skyylarkk/projet3A/Modele_Solidworks/Pince/Pièce1.SLDPRT

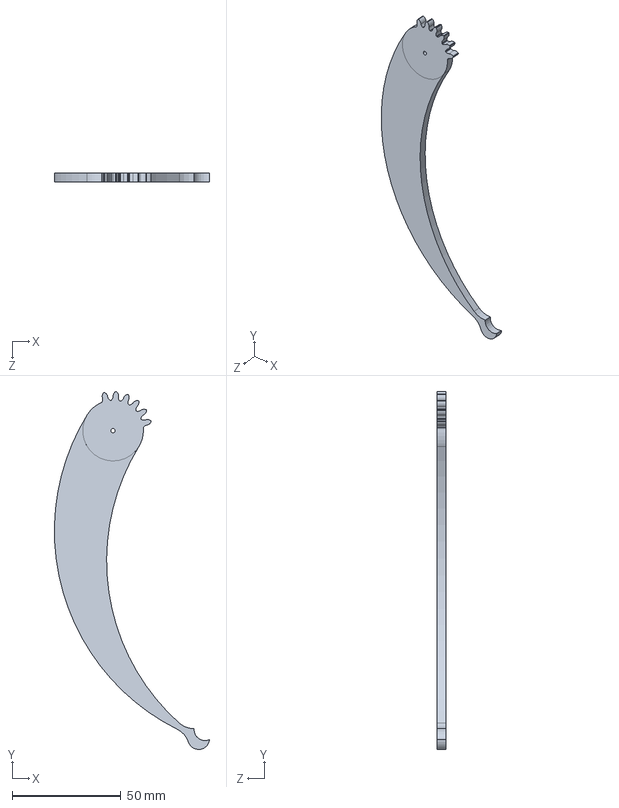
[picture p39: CAD file, 2022-12-07]
Modele_Solidworks/Pince/Pièce1.SLDPRT
71.2 x 164.3 x 4.00 mm
