skyylarkk/projet3A/Modele_Solidworks/Avant-bras/Support_axe_2.SLDPRT

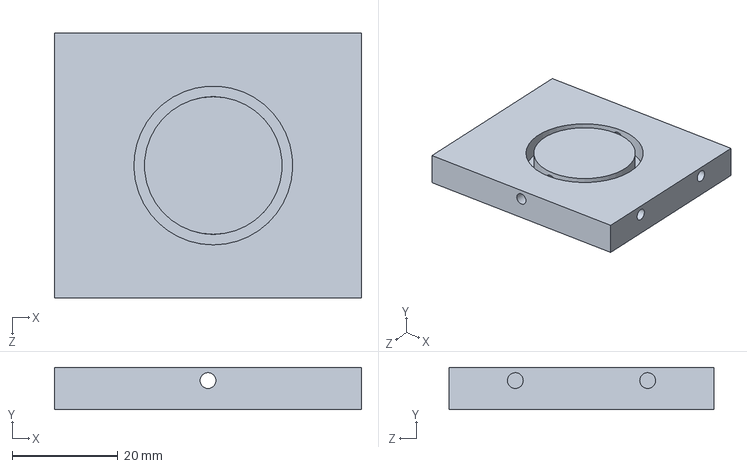
[picture p40: CAD file, 2022-12-26]
Modele_Solidworks/Avant-bras/Support_axe_2.SLDPRT
58.0 x 8.00 x 50.0 mm
