skyylarkk/projet3A/Modele_Solidworks/Base/roue sur pignon moteur.SLDPRT

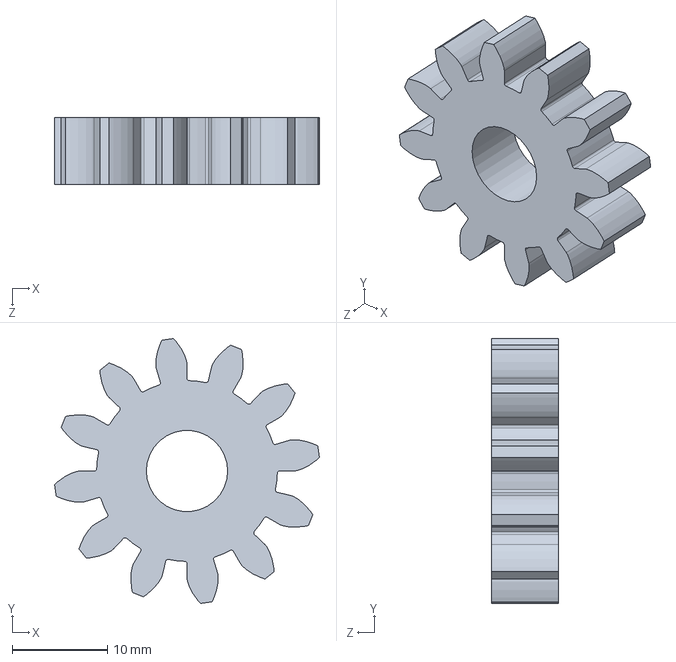
[picture p41: CAD file, 2023-01-16]
Modele_Solidworks/Base/roue sur pignon moteur.SLDPRT
27.9 x 27.9 x 7.00 mm
