skyylarkk/projet3A/Modele_Solidworks/Epaule/roue satellite.SLDPRT

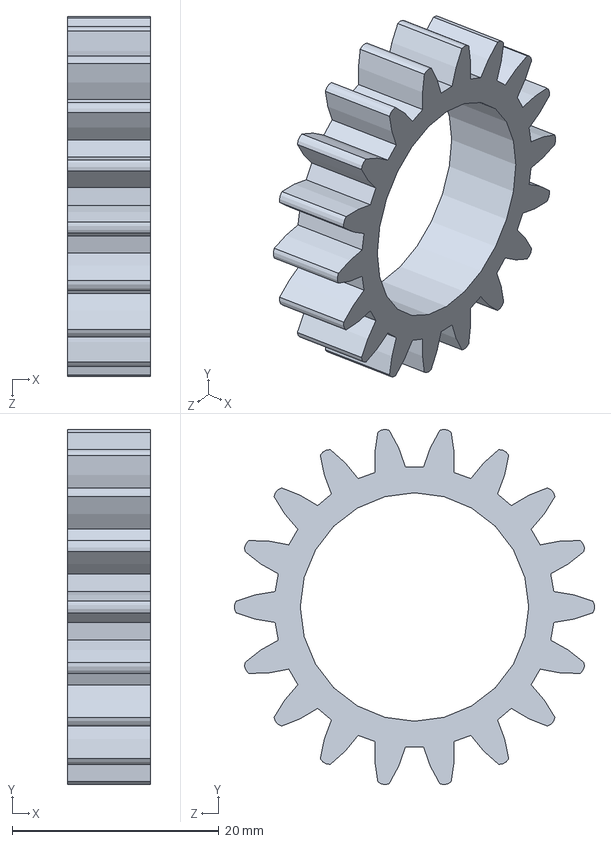
[picture p42: CAD file, 2023-01-16]
Modele_Solidworks/Epaule/roue satellite.SLDPRT
8.00 x 34.4 x 34.8 mm
