skyylarkk/projet3A/Modele_Solidworks/Pince/Bloqueur.SLDPRT

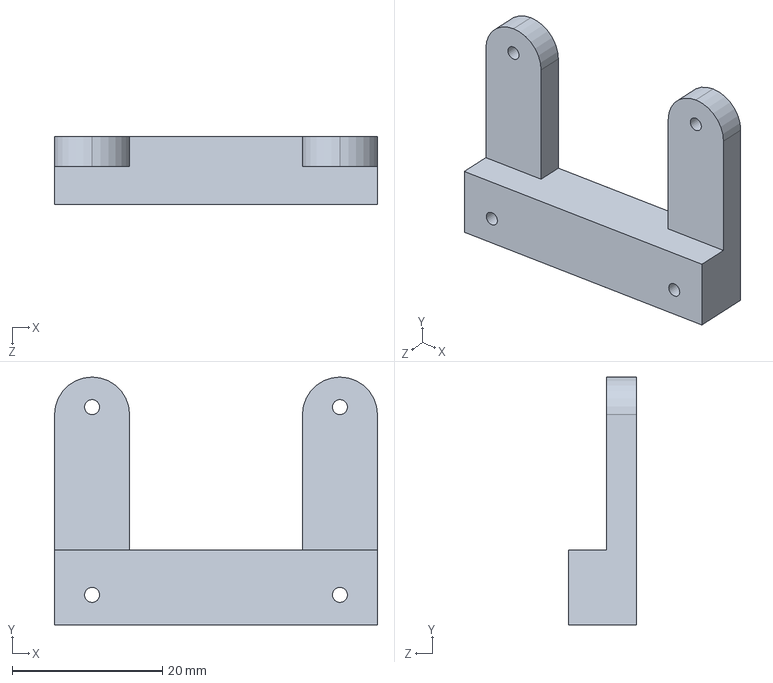
[picture p43: CAD file, 2022-12-07]
Modele_Solidworks/Pince/Bloqueur.SLDPRT
43.0 x 33.0 x 9.00 mm
