skyylarkk/projet3A/Modele_Solidworks/Poignet/Côté_2_ext - Copie.SLDPRT

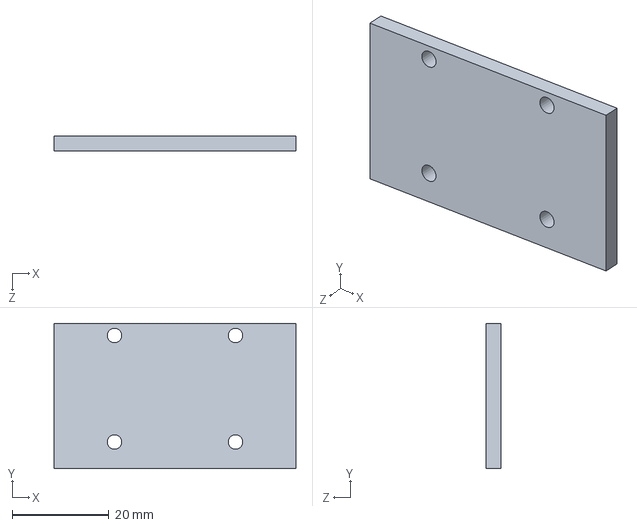
[picture p44: CAD file, 2022-12-11]
Modele_Solidworks/Poignet/Côté_2_ext - Copie.SLDPRT
50.0 x 30.0 x 3.00 mm
