skyylarkk/projet3A/Modele_Solidworks/Bras/Support_axe.SLDPRT

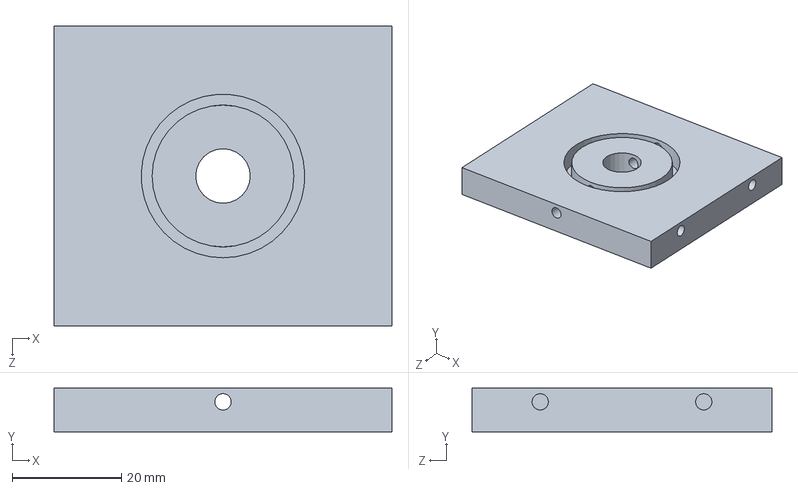
[picture p45: CAD file, 2023-01-06]
Modele_Solidworks/Bras/Support_axe.SLDPRT
62.0 x 8.00 x 55.0 mm
