skyylarkk/projet3A/Modele_Solidworks/Epaule/Couronne train epi.SLDPRT

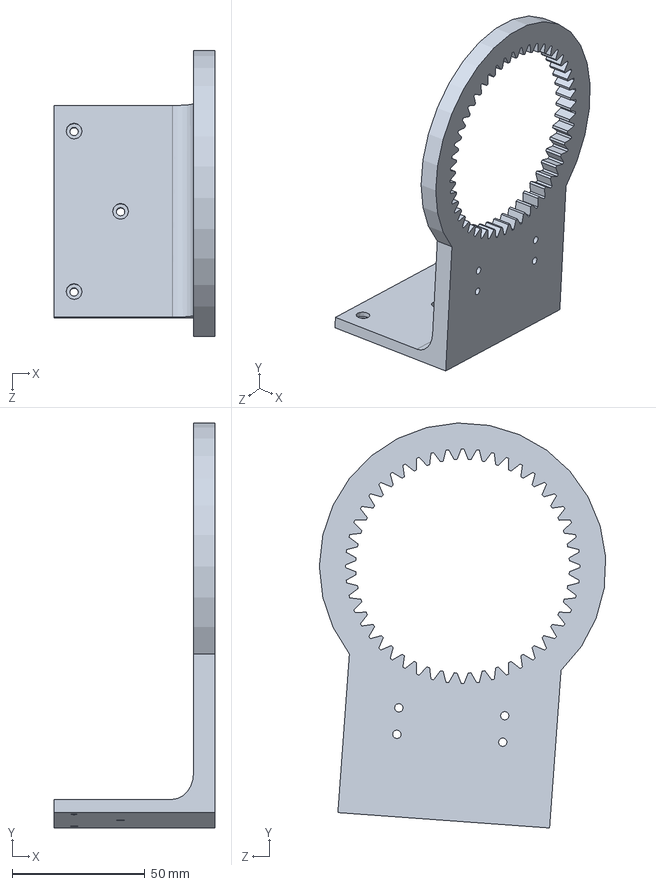
[picture p46: CAD file, 2023-01-16]
Modele_Solidworks/Epaule/Couronne train epi.SLDPRT
60.5 x 152.6 x 107.9 mm
