skyylarkk/projet3A/Modele_Solidworks/Poignet/Support_axe_2.SLDPRT

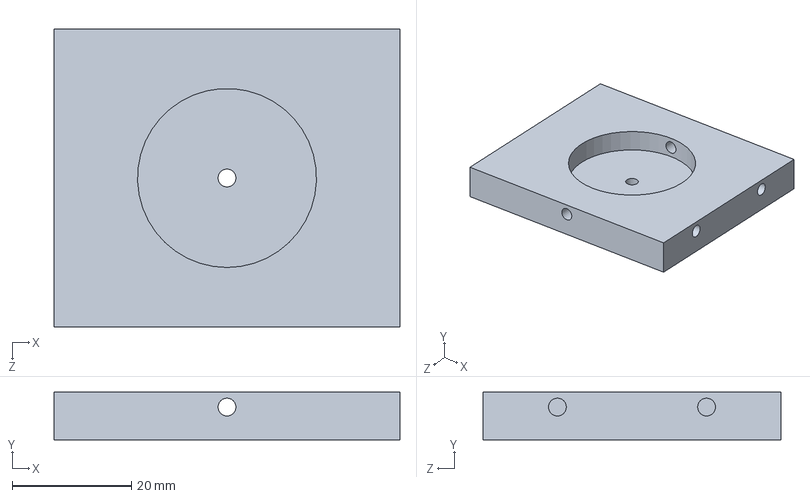
[picture p47: CAD file, 2022-12-11]
Modele_Solidworks/Poignet/Support_axe_2.SLDPRT
58.0 x 8.00 x 50.0 mm
