skyylarkk/projet3A/Modele_Solidworks/Base/bearing_61804_2_02.SLDPRT

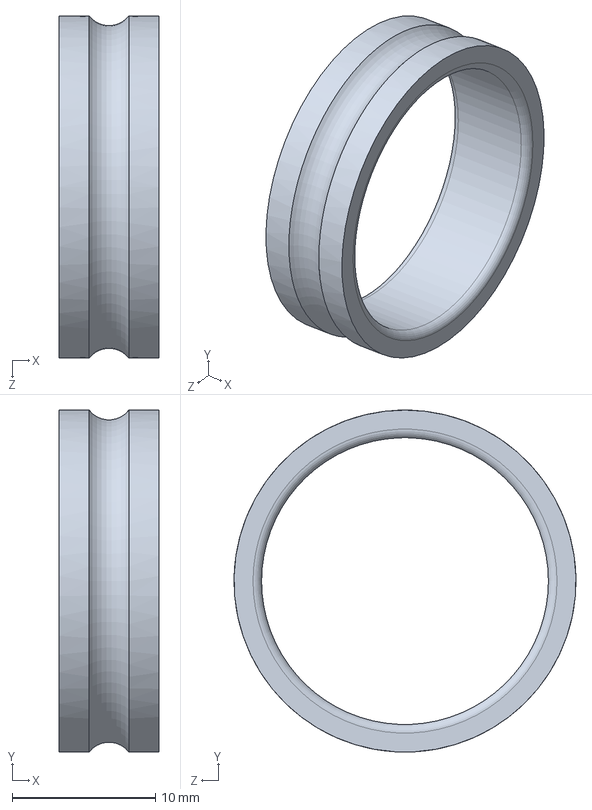
[picture p48: CAD file, 2023-01-10]
Modele_Solidworks/Base/bearing_61804_2_02.SLDPRT
7.00 x 23.8 x 23.9 mm
