skyylarkk/projet3A/Modele_Solidworks/Bras/Côté_ext.SLDPRT

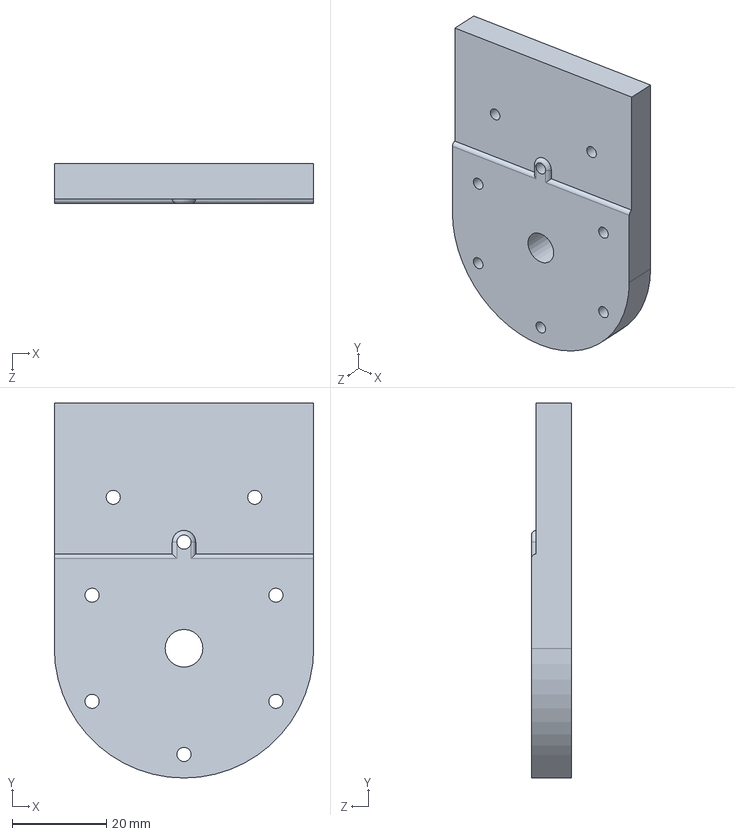
[picture p49: CAD file, 2023-01-06]
Modele_Solidworks/Bras/Côté_ext.SLDPRT
55.0 x 79.5 x 8.50 mm
