skyylarkk/projet3A/Modele_Solidworks/Epaule/satellite.SLDPRT

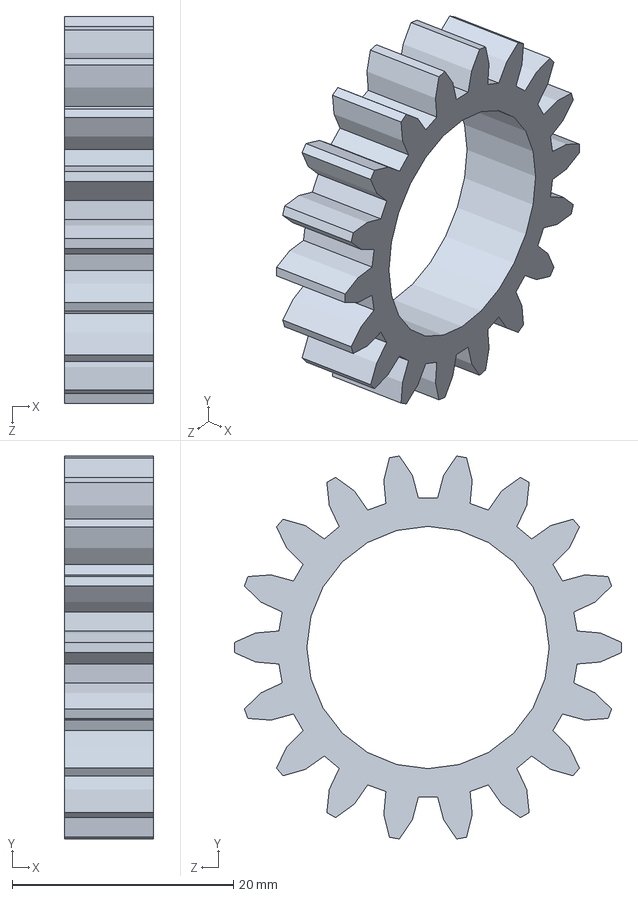
[picture p50: CAD file, 2023-01-16]
Modele_Solidworks/Epaule/satellite.SLDPRT
8.00 x 34.6 x 35.0 mm
