skyylarkk/projet3A/Modele_Solidworks/Poignet/Carcasse - Copie.SLDPRT

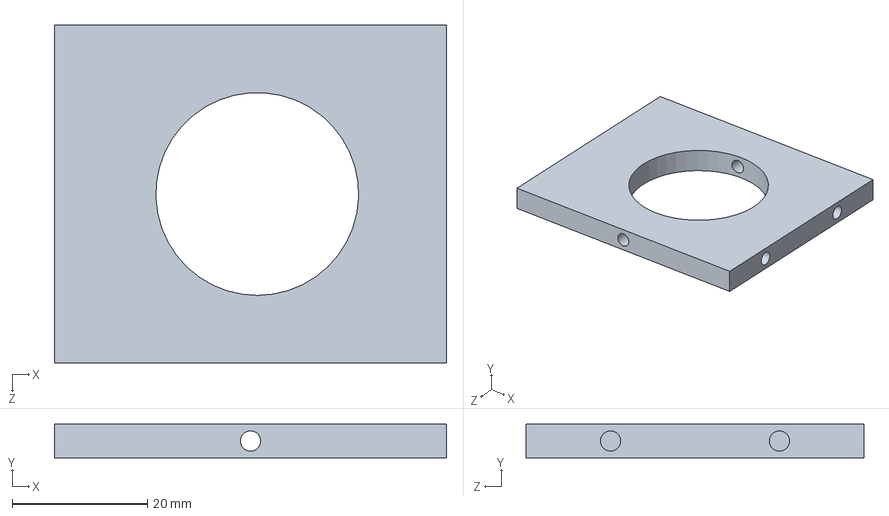
[picture p51: CAD file, 2022-12-11]
Modele_Solidworks/Poignet/Carcasse - Copie.SLDPRT
58.0 x 5.00 x 50.0 mm
