skyylarkk/projet3A/Modele_Solidworks/Base/base bati1.SLDPRT

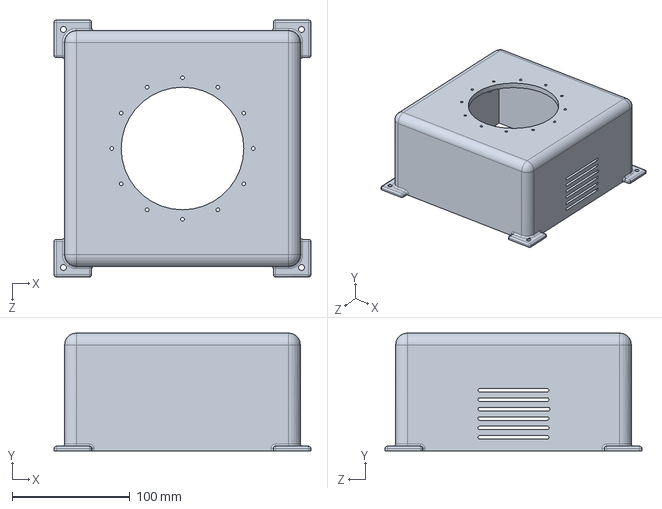
[picture p52: CAD file, 2023-01-10]
Modele_Solidworks/Base/base bati1.SLDPRT
218.0 x 100.0 x 218.0 mm
