skyylarkk/projet3A/Modele_Solidworks/Bras/Carcasse.SLDPRT

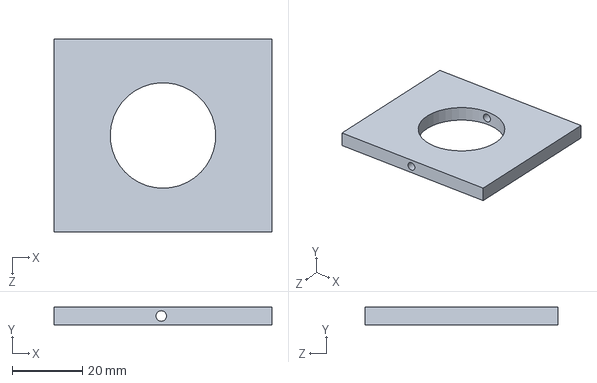
[picture p53: CAD file, 2023-01-06]
Modele_Solidworks/Bras/Carcasse.SLDPRT
62.0 x 5.00 x 55.0 mm
