skyylarkk/projet3A/Modele_Solidworks/Epaule/roue sortie porte satellite.SLDPRT

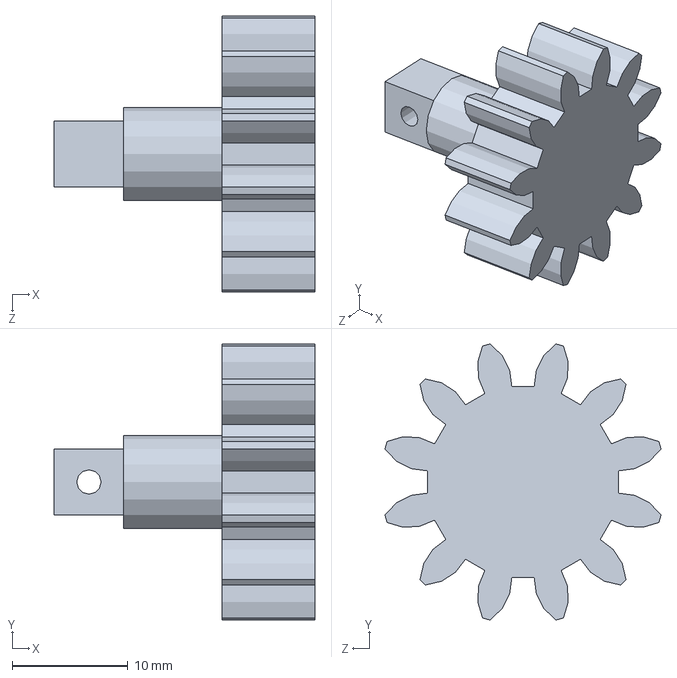
[picture p54: CAD file, 2023-01-16]
Modele_Solidworks/Epaule/roue sortie porte satellite.SLDPRT
22.5 x 23.8 x 23.8 mm
