skyylarkk/projet3A/Modele_Solidworks/Avant-bras/Support_axe.SLDPRT

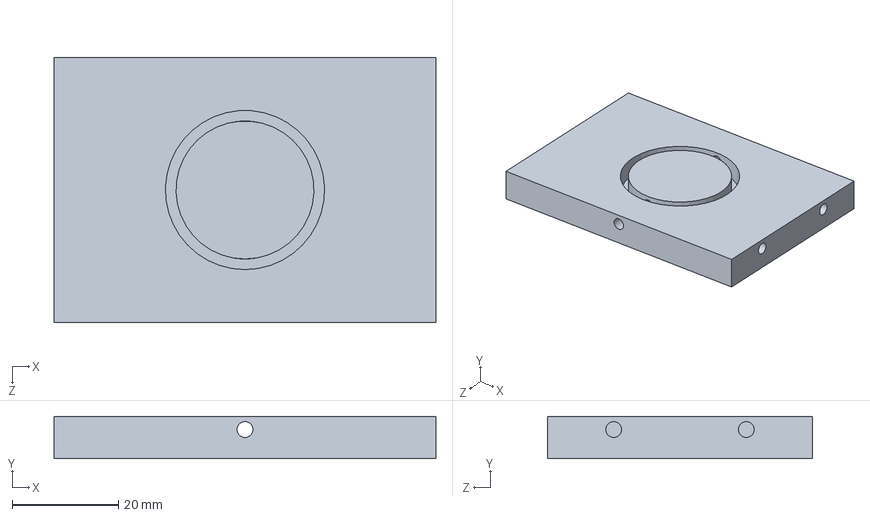
[picture p55: CAD file, 2022-12-26]
Modele_Solidworks/Avant-bras/Support_axe.SLDPRT
72.0 x 8.00 x 50.0 mm
