skyylarkk/projet3A/Modele_Solidworks/Base/bearing_61804_2_01.SLDPRT

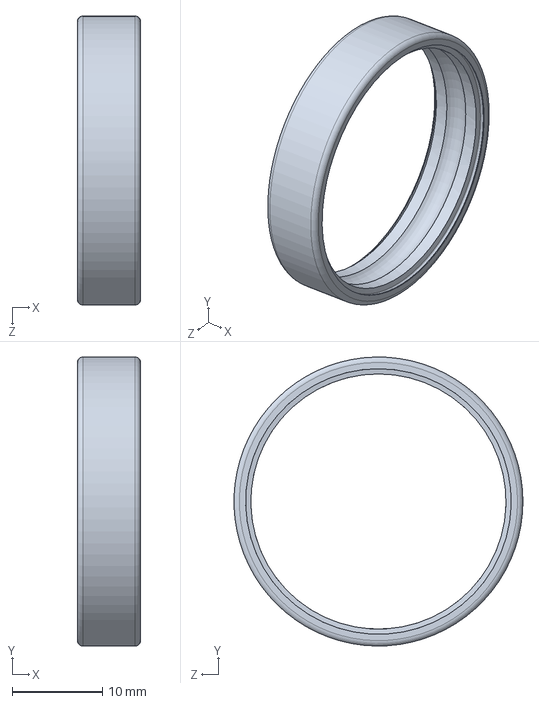
[picture p56: CAD file, 2023-01-10]
Modele_Solidworks/Base/bearing_61804_2_01.SLDPRT
7.00 x 32.0 x 32.0 mm
