skyylarkk/projet3A/Modele_Solidworks/Epaule/planetaire 1 pignon moteur.SLDPRT

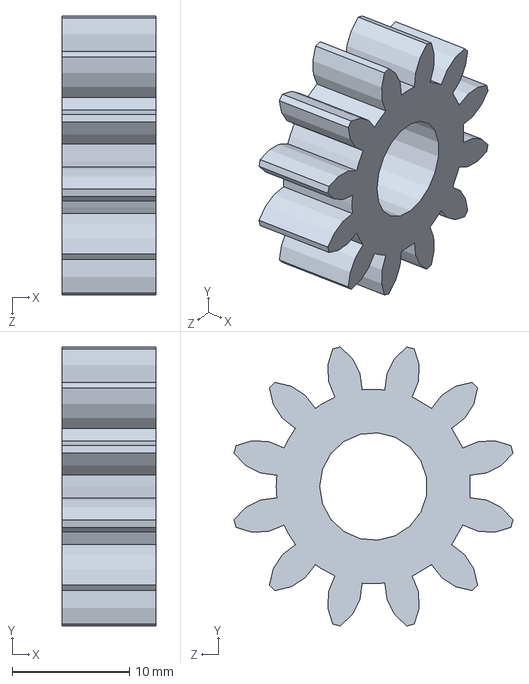
[picture p57: CAD file, 2023-01-16]
Modele_Solidworks/Epaule/planetaire 1 pignon moteur.SLDPRT
8.00 x 23.8 x 23.8 mm
