skyylarkk/projet3A/Modele_Solidworks/Epaule/roue sorti de reducteur.SLDPRT

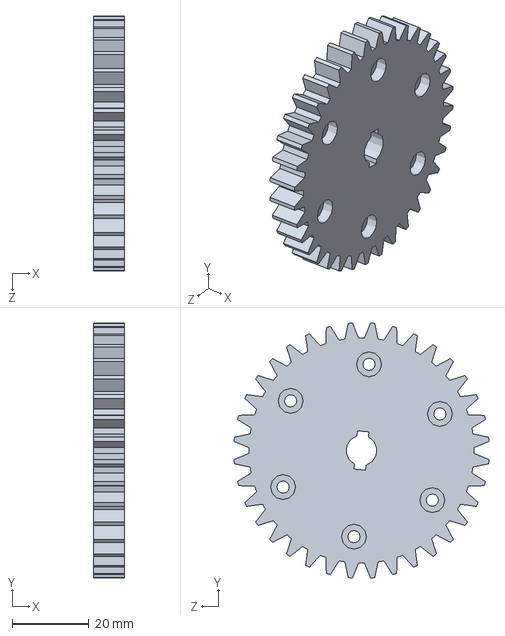
[picture p58: CAD file, 2023-01-16]
Modele_Solidworks/Epaule/roue sorti de reducteur.SLDPRT
8.00 x 66.3 x 66.3 mm
