skyylarkk/projet3A/Modele_Solidworks/Pince/Base.SLDPRT

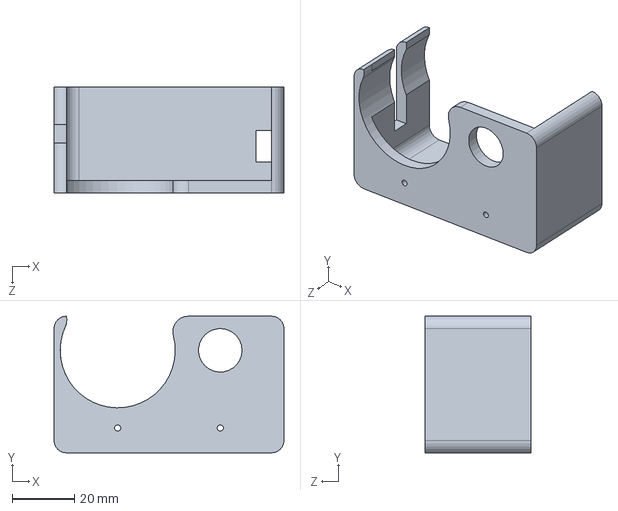
[picture p59: CAD file, 2022-11-30]
Modele_Solidworks/Pince/Base.SLDPRT
74.0 x 44.0 x 34.0 mm
