skyylarkk/projet3A/Modele_Solidworks/Avant-bras/Côté_ext.SLDPRT

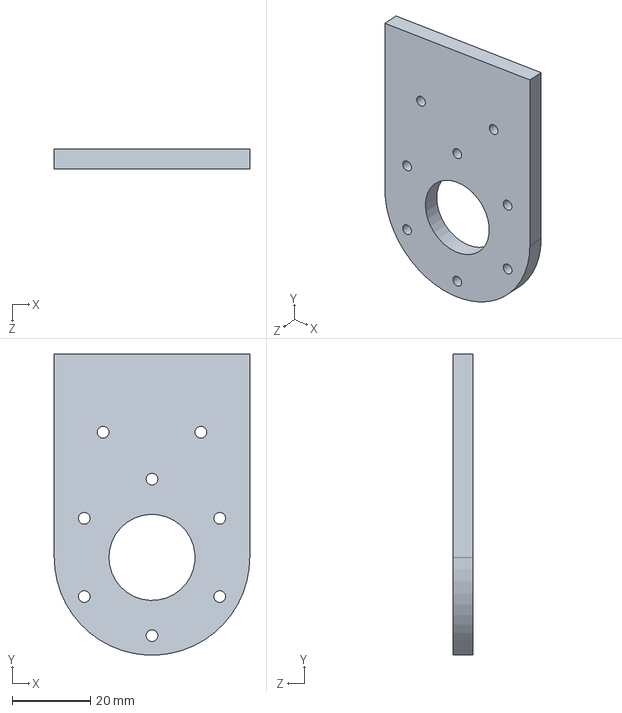
[picture p60: CAD file, 2022-12-26]
Modele_Solidworks/Avant-bras/Côté_ext.SLDPRT
50.0 x 77.0 x 5.00 mm
