skyylarkk/projet3A/Modele_Solidworks/Base/bearing_61804_2_03.SLDPRT

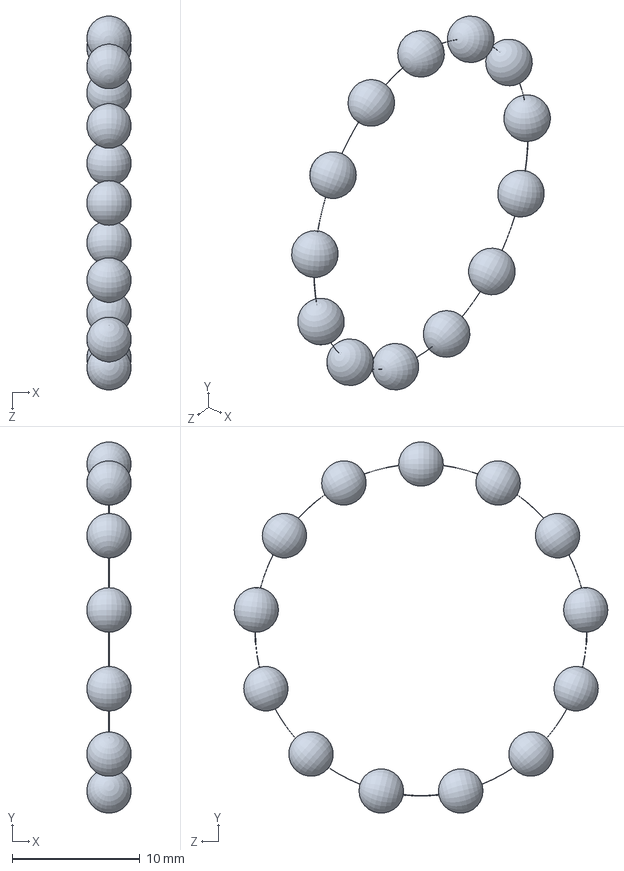
[picture p61: CAD file, 2023-01-10]
Modele_Solidworks/Base/bearing_61804_2_03.SLDPRT
3.47 x 29.1 x 29.3 mm
