skyylarkk/projet3A/Modele_Solidworks/Epaule/base epaule.SLDPRT

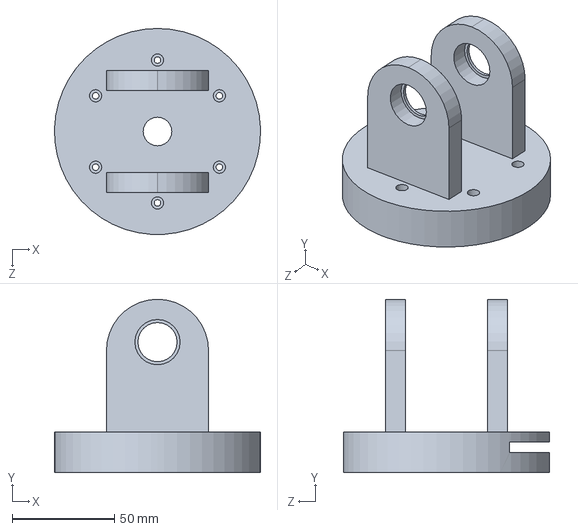
[picture p62: CAD file, 2023-01-10]
Modele_Solidworks/Epaule/base epaule.SLDPRT
100.9 x 85.0 x 101.0 mm
