skyylarkk/projet3A/Modele_Solidworks/Avant-bras/Carcasse.SLDPRT

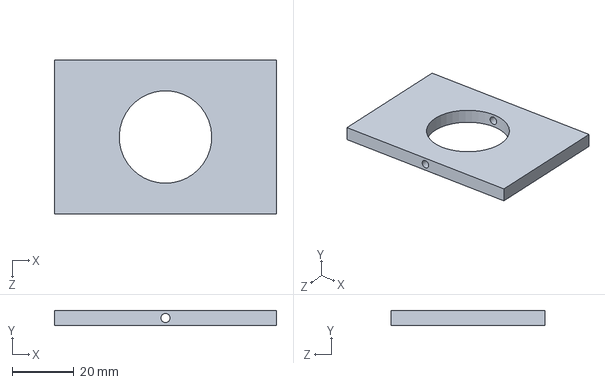
[picture p63: CAD file, 2022-12-26]
Modele_Solidworks/Avant-bras/Carcasse.SLDPRT
72.0 x 5.00 x 50.0 mm
