skyylarkk/projet3A/Modele_Solidworks/Base/plateau.SLDPRT

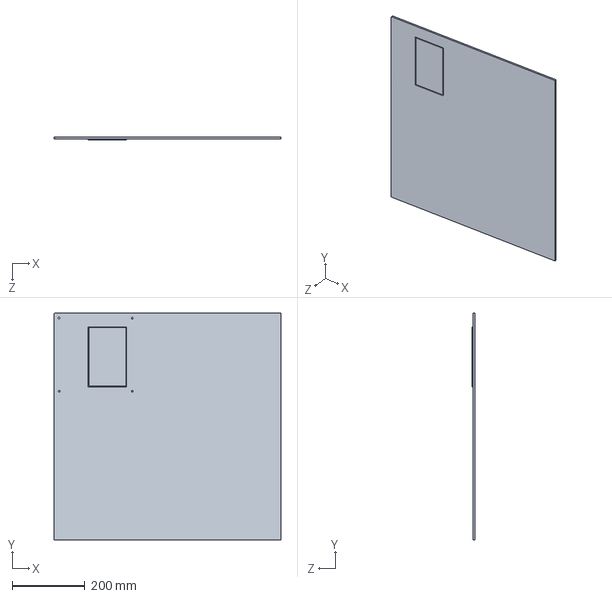
[picture p64: CAD file, 2023-01-05]
Modele_Solidworks/Base/plateau.SLDPRT
626.0 x 626.0 x 8.00 mm
