skyylarkk/projet3A/Modele_Solidworks/Base/base bati 2.SLDPRT

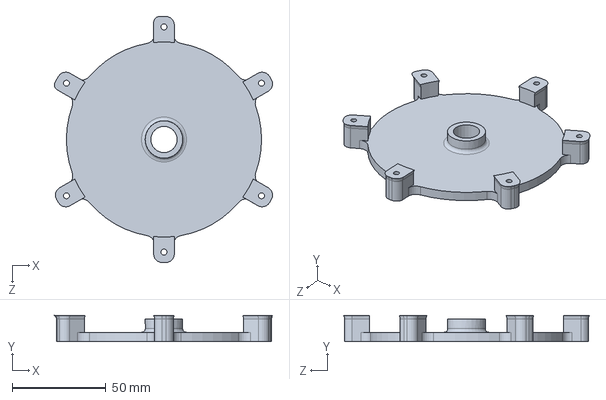
[picture p65: CAD file, 2022-11-30]
Modele_Solidworks/Base/base bati 2.SLDPRT
116.2 x 14.0 x 131.1 mm
