skyylarkk/projet3A/Modele_Solidworks/Base/carte.SLDPRT

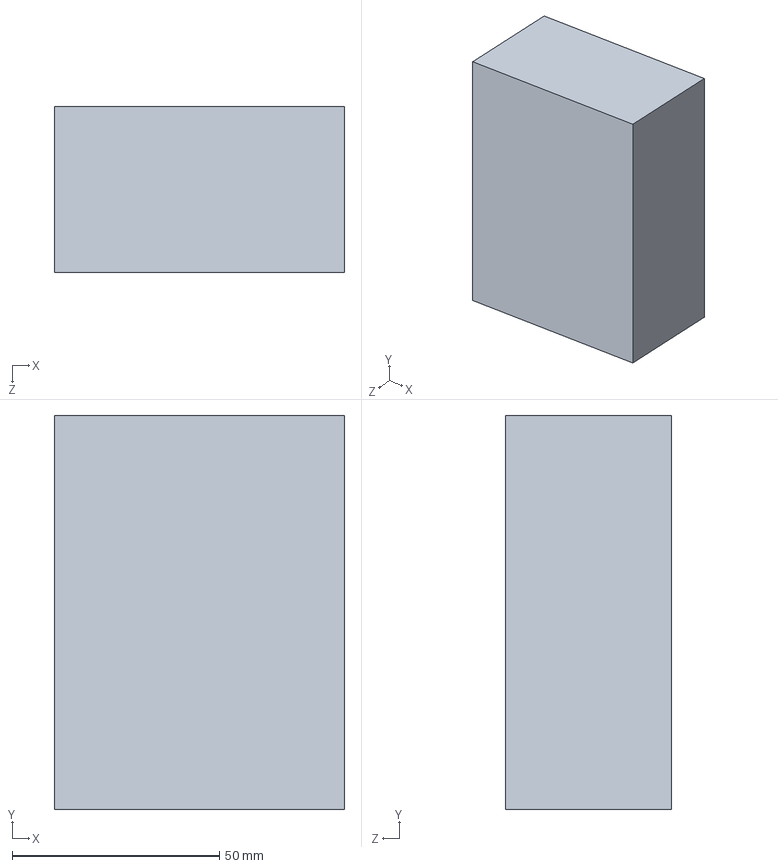
[picture p66: CAD file, 2022-11-30]
Modele_Solidworks/Base/carte.SLDPRT
70.0 x 95.0 x 40.0 mm
