skyylarkk/projet3A/Modele_Solidworks/Base/transfo.SLDPRT

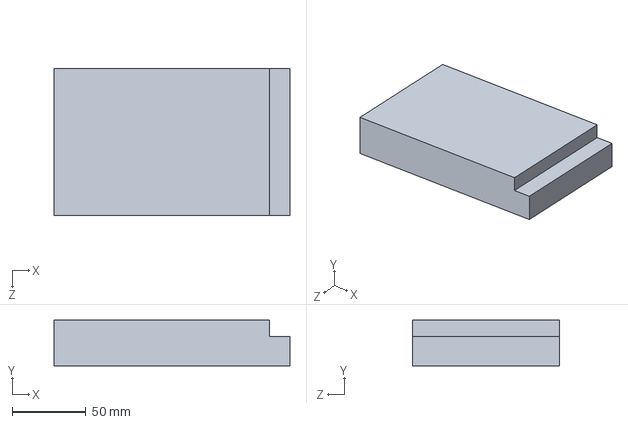
[picture p67: CAD file, 2022-11-30]
Modele_Solidworks/Base/transfo.SLDPRT
160.0 x 31.0 x 100.0 mm
