skyylarkk/projet3A/Modele_Solidworks/Epaule/PM55L-048.SLDPRT

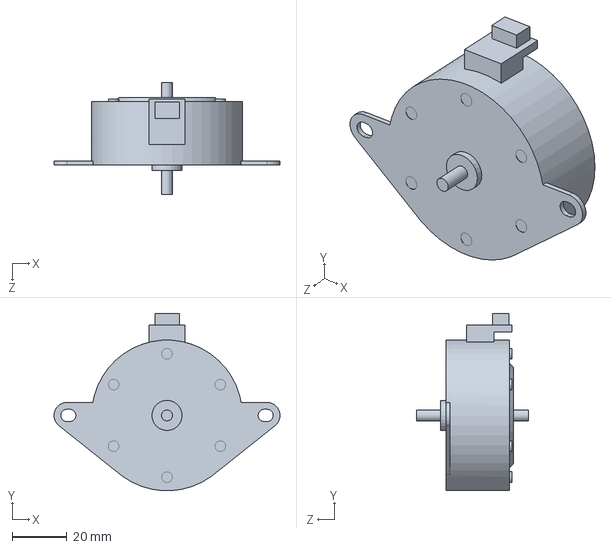
[picture p68: CAD file, 2023-01-05]
Modele_Solidworks/Epaule/PM55L-048.SLDPRT
82.5 x 64.7 x 41.0 mm
