skyylarkk/projet3A/Modele_Solidworks/Epaule/support axe support planetaire.SLDPRT

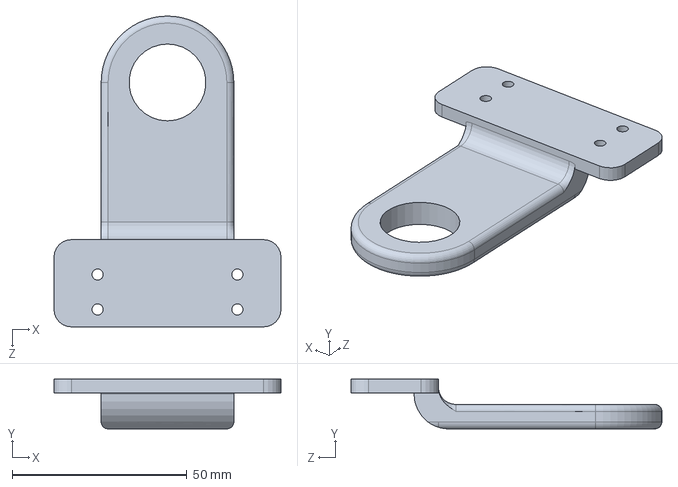
[picture p69: CAD file, 2022-12-28]
Modele_Solidworks/Epaule/support axe support planetaire.SLDPRT
65.0 x 14.2 x 89.0 mm
