skyylarkk/projet3A/Modele_Solidworks/Epaule/support moteur.SLDPRT

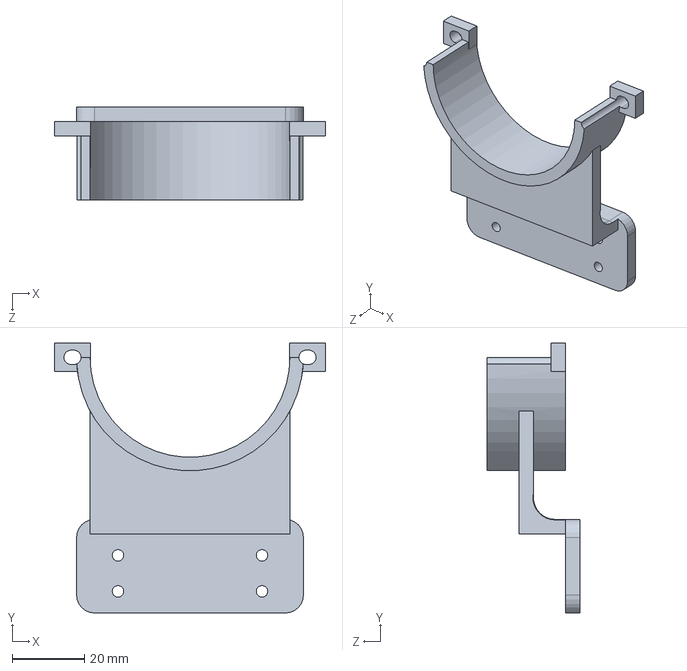
[picture p70: CAD file, 2022-12-28]
Modele_Solidworks/Epaule/support moteur.SLDPRT
75.2 x 75.0 x 25.7 mm
