skyylarkk/projet3A/Modele_Solidworks/Epaule/support planetaire part2.SLDPRT

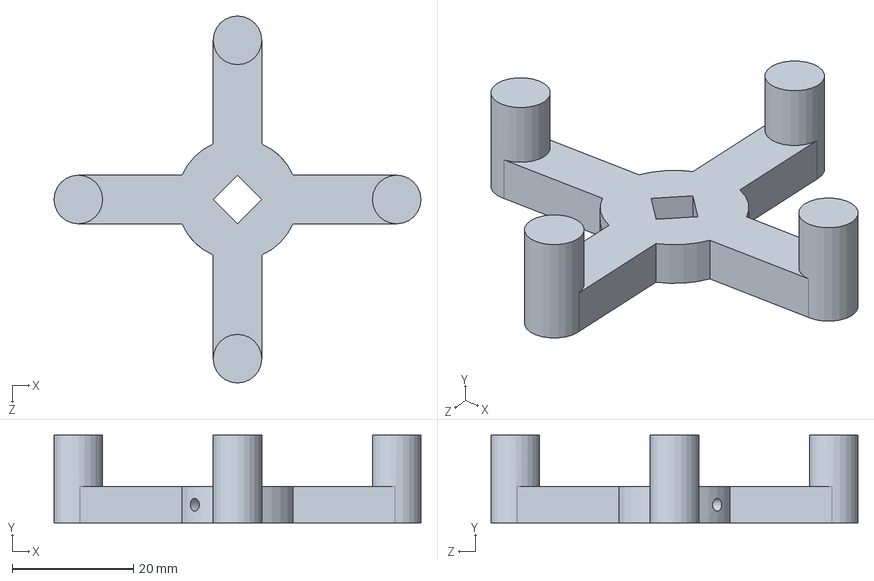
[picture p71: CAD file, 2022-12-21]
Modele_Solidworks/Epaule/support planetaire part2.SLDPRT
60.5 x 14.5 x 60.5 mm
